JohnMLarkin/FlightComputer-HW/Components-3D_Printed/STL Files/breadboard clip.stl

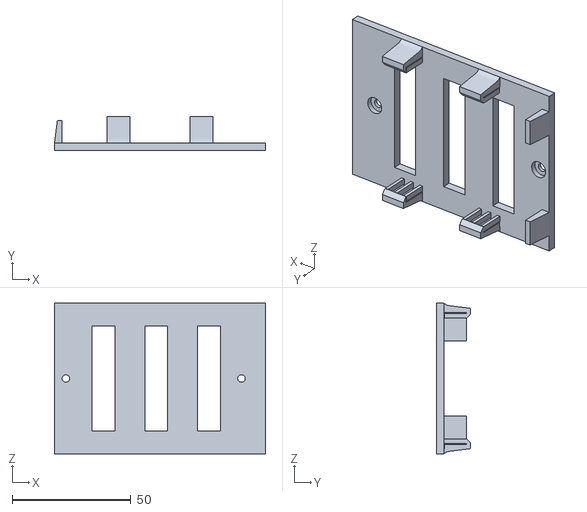
[picture p17: CAD file, 2019-05-28]
Components-3D_Printed/STL Files/breadboard clip.stl
88.9 x 14.3 x 63.5
