JohnMLarkin/FlightComputer-HW/Components-3D_Printed/STL Files/power channel.stl

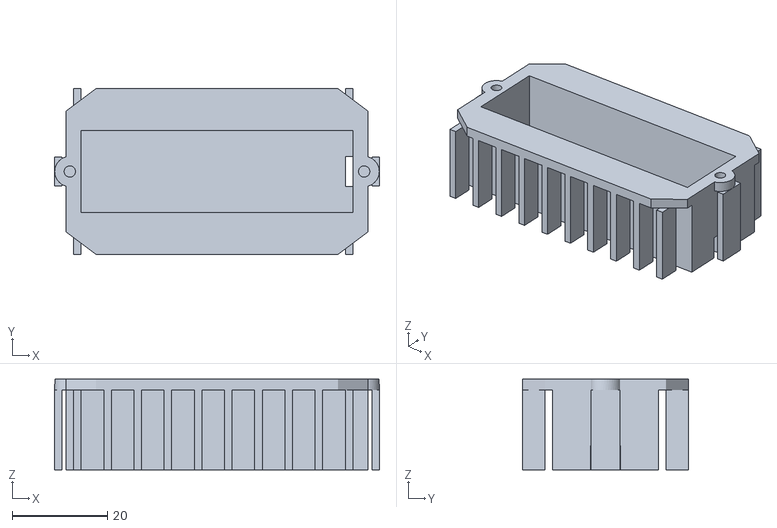
[picture p18: CAD file, 2019-05-28]
Components-3D_Printed/STL Files/power channel.stl
68.4 x 34.9 x 19.0
