JohnMLarkin/FlightComputer-HW/Components-3D_Printed/STL Files/bottom layer cap.stl

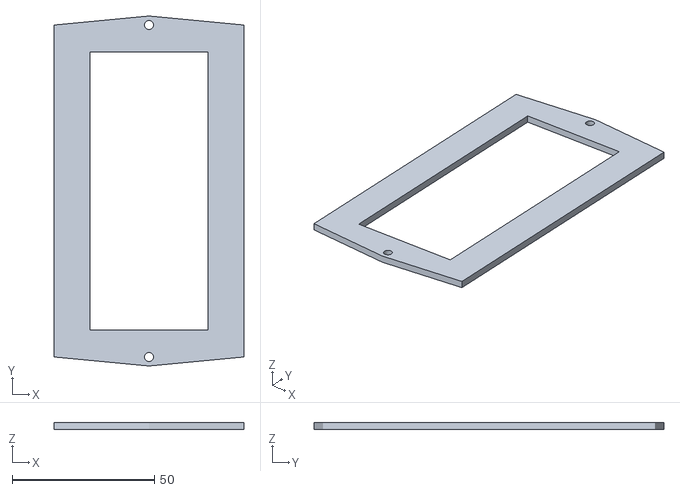
[picture p19: CAD file, 2019-05-28]
Components-3D_Printed/STL Files/bottom layer cap.stl
66.7 x 122.9 x 2.54
