JohnMLarkin/FlightComputer-HW/Components-3D_Printed/STL Files/bottom layer ctrl pod.stl

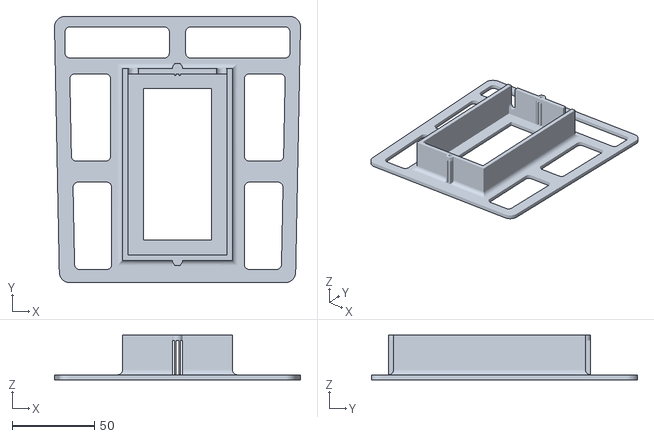
[picture p20: CAD file, 2019-05-28]
Components-3D_Printed/STL Files/bottom layer ctrl pod.stl
149.6 x 161.9 x 27.2
